ljungqvistaxel/gridcap/software/calculations/plots/capacitance_spread_07.png

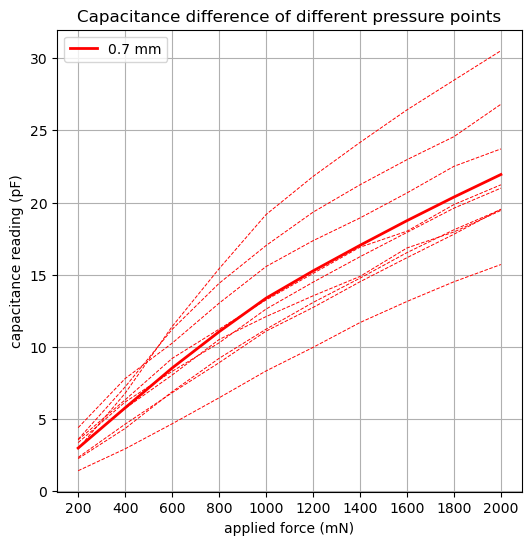
software/calculations/plots/capacitance_spread_07.png
