ljungqvistaxel/gridcap/software/uart_host/include/mux_map.h

#ifndef MUX_MAP_H
#define MUX_MAP_H

/* Maps mux index to pad index. 0-15 is mux 1, 16-31 is mux 2, etc. */
int mux_map[64] = {
/*   0   1   2   3   4   5   6   7   8   9  10  11  12  13  14  15  */
    11,  3, 10,  2,  1,  9,  0,  8, 16, 24, 17, 25, 26, 18, 27, 19, // MUX1
    15,  7, 14,  6,  5, 13,  4, 12, 20, 28, 21, 29, 30, 22, 31, 23, // MUX2
    43, 35, 42, 34, 33, 41, 32, 40, 48, 56, 49, 57, 58, 50, 59, 51, // MUX3
    47, 39, 46, 38, 37, 45, 36, 44, 52, 60, 53, 61, 62, 54, 63, 55  // MUX4
};

#endif
